felixstdp/raptor/raptor_pro/evo/soporte_cables.scad

$fn=30;
difference(){
union(){
cube([10,20,2]);
translate([0,5,0])rotate([0,90,0])
hull(){
cylinder(d=4,h=10);
translate([0,10,0])cylinder(d=4,h=10);
}
}
translate([0,5,0])rotate([0,90,0])
{
translate([0,0,-1])cylinder(d=2,h=12);
translate([0,10,-1])cylinder(d=2,h=12);
}
}
